winsim/Vol-Box/pictures/mochup-v1/20170902_012305.jpg

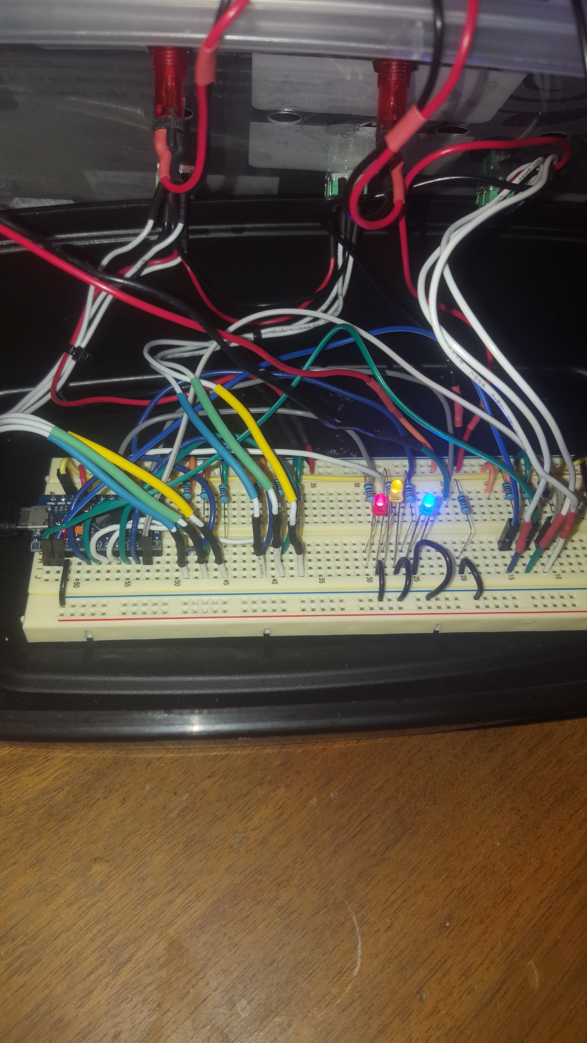
pictures/mochup-v1/20170902_012305.jpg
