winsim/Vol-Box/pictures/mochup-v1/20170902_012146.jpg

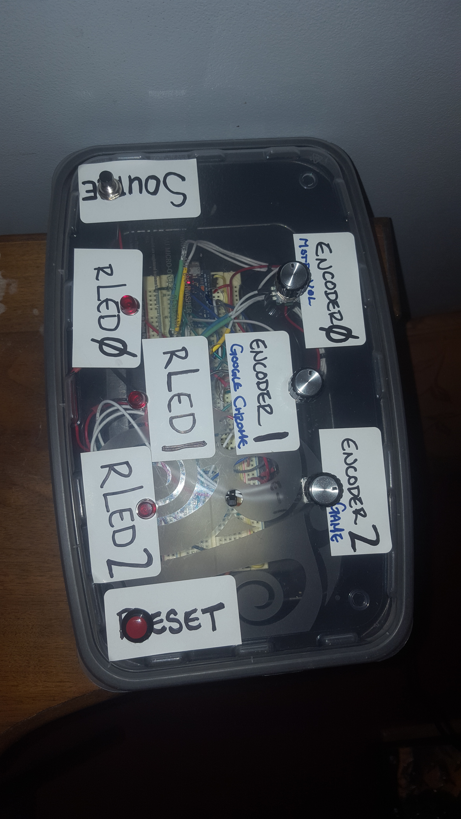
pictures/mochup-v1/20170902_012146.jpg
